abdelrahman-a-shahin/Space-Observatory-Microsatellite-AOCS-Testbed/EGOS_1_Firmware_mgt/stl_model.h

#pragma once
#include <pgmspace.h>

static const uint32_t STL_SIZE = 24084;

static const uint8_t STL_DATA[] PROGMEM = {
  0x43, 0x4F, 0x4C, 0x4F, 0x52, 0x3D, 0x7F, 0x7F, 0x7F, 0x20, 0x4D, 0x41, 0x54, 0x45, 0x52, 0x49,
  0x41, 0x4C, 0x3D, 0x7F, 0x7F, 0x7F, 0x20, 0x7F, 0x7F, 0x7F, 0x20, 0x7F, 0x7F, 0x7F, 0x20, 0x20,
  0x20, 0x20, 0x20, 0x20, 0x20, 0x20, 0x20, 0x20, 0x20, 0x20, 0x20, 0x20, 0x20, 0x20, 0x20, 0x20,
  0x20, 0x20, 0x20, 0x20, 0x20, 0x20, 0x20, 0x20, 0x20, 0x20, 0x20, 0x20, 0x20, 0x20, 0x20, 0x20,
  0x20, 0x20, 0x20, 0x20, 0x20, 0x20, 0x20, 0x20, 0x20, 0x20, 0x20, 0x20, 0x20, 0x20, 0x20, 0x20,
  0xE0, 0x01, 0x00, 0x00, 0xB3, 0x41, 0x96, 0x3B, 0x0F, 0xFF, 0x7F, 0xBF, 0x05, 0xD9, 0x35, 0xBB,
  0x33, 0x33, 0x32, 0x43, 0xC5, 0x59, 0xB4, 0x42, 0xFC, 0x02, 0x69, 0x42, 0x00, 0x00, 0x48, 0x43,
  0xA8, 0x8F, 0xB4, 0x42, 0xA9, 0x65, 0x61, 0x42, 0x3A, 0xAB, 0x47, 0x43, 0xB9, 0x1E, 0xB4, 0x42,
  0x2B, 0x4B, 0x07, 0x43, 0x00, 0x00, 0x28, 0x0B, 0x9B, 0x3B, 0x02, 0xFF, 0x7F, 0xBF, 0xFE, 0x83,
  0x38, 0xBB, 0x3A, 0xAB, 0x47, 0x43, 0xB9, 0x1E, 0xB4, 0x42, 0x2B, 0x4B, 0x07, 0x43, 0x0F, 0x00,
  0xF0, 0x42, 0x6E, 0xB5, 0xB2, 0x42, 0x91, 0x08, 0x7C, 0x43, 0x33, 0x33, 0x32, 0x43, 0xC5, 0x59,
  0xB4, 0x42, 0xFC, 0x02, 0x69, 0x42, 0x00, 0x00, 0x97, 0x33, 0x27, 0x3C, 0x8F, 0xFC, 0x7F, 0xBF,
  0x2A, 0x39, 0x71, 0x3A, 0x0D, 0x31, 0x47, 0x43, 0x10, 0x46, 0xB4, 0x42, 0x25, 0x16, 0x60, 0x43,
  0x0F, 0x00, 0xF0, 0x42, 0x6E, 0xB5, 0xB2, 0x42, 0x91, 0x08, 0x7C, 0x43, 0x3A, 0xAB, 0x47, 0x43,
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
  0x33, 0x33, 0x32, 0x43, 0xC5, 0x59, 0xB4, 0x42, 0xFC, 0x02, 0x69, 0x42, 0x01, 0x00, 0xF0, 0x42,
  0x6E, 0xB5, 0xB5, 0x42, 0xA2, 0x7F, 0x91, 0x42, 0x00, 0x00, 0xCB, 0xA7, 0x81, 0xBD, 0x31, 0x13,
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
};
